thelowprokill/nerdboard/images/6.2/PXL_20240111_174422805.jpg

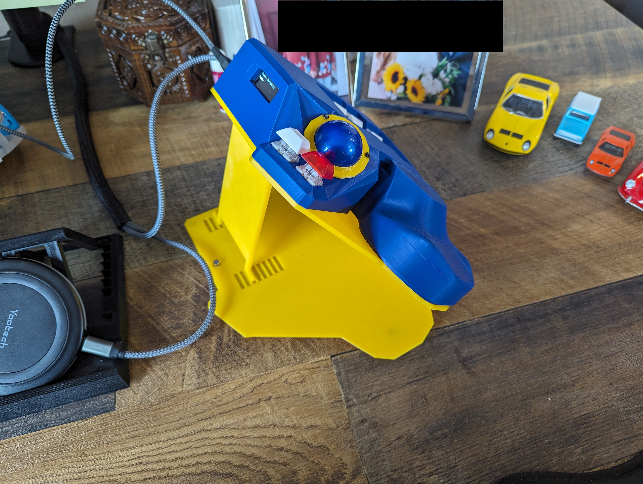
images/6.2/PXL_20240111_174422805.jpg
