thelowprokill/nerdboard/images/6.2/PXL_20240111_174425794.jpg

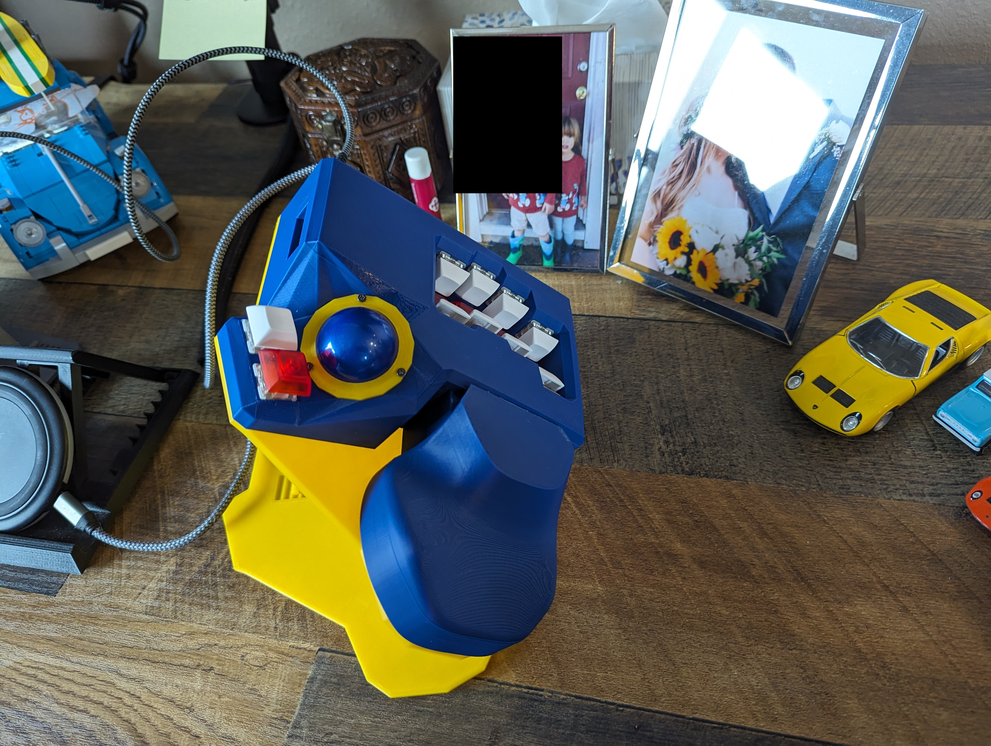
images/6.2/PXL_20240111_174425794.jpg
