thelowprokill/nerdboard/images/6.2/PXL_20240111_174430788.jpg

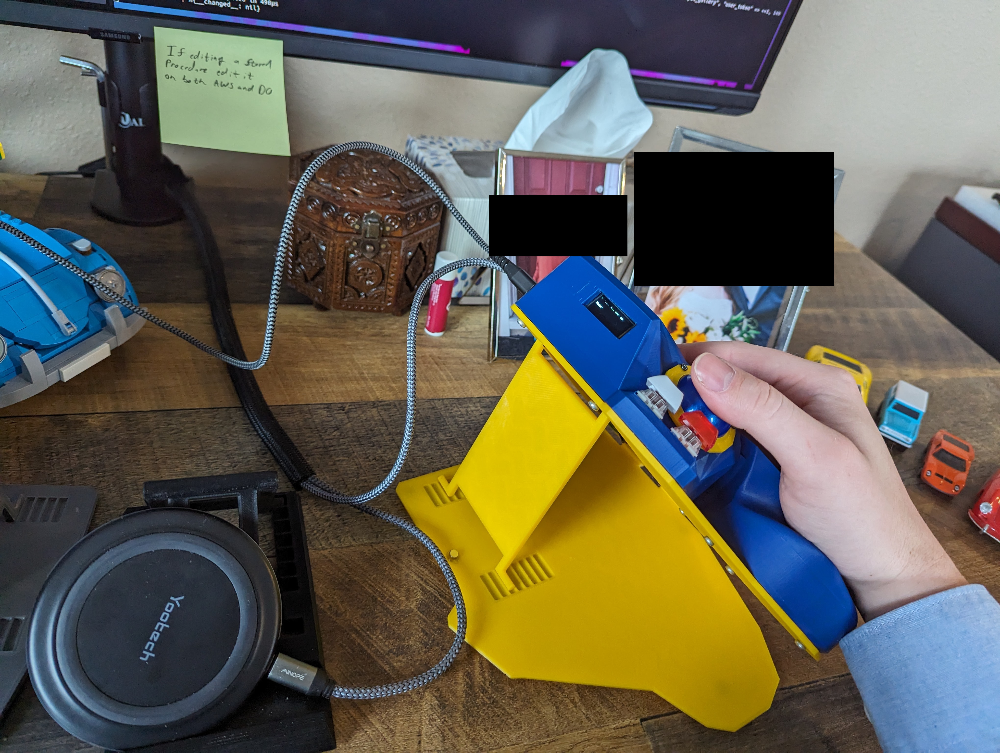
images/6.2/PXL_20240111_174430788.jpg
