thelowprokill/nerdboard/images/6.2/PXL_20240308_211952683.jpg

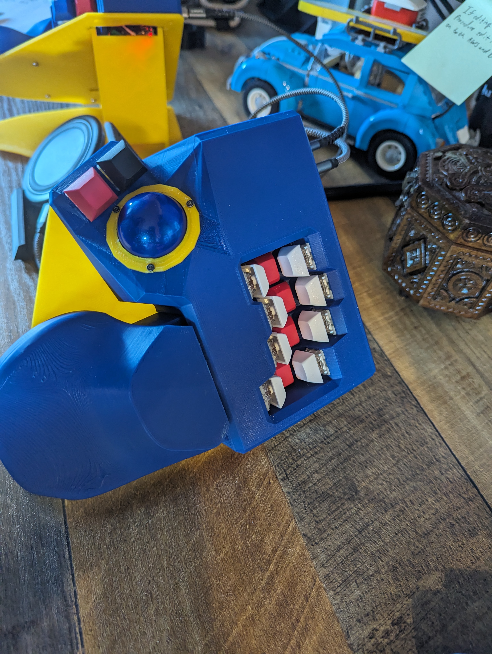
images/6.2/PXL_20240308_211952683.jpg
