thelowprokill/nerdboard/images/6.2/PXL_20240308_211957653.jpg

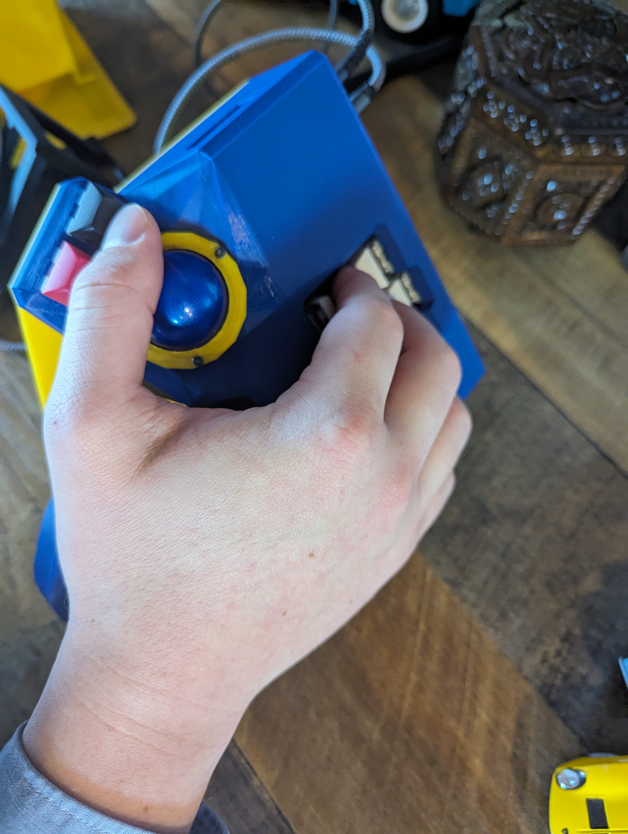
images/6.2/PXL_20240308_211957653.jpg
