thelowprokill/nerdboard/images/6.2/PXL_20240308_212002990.jpg

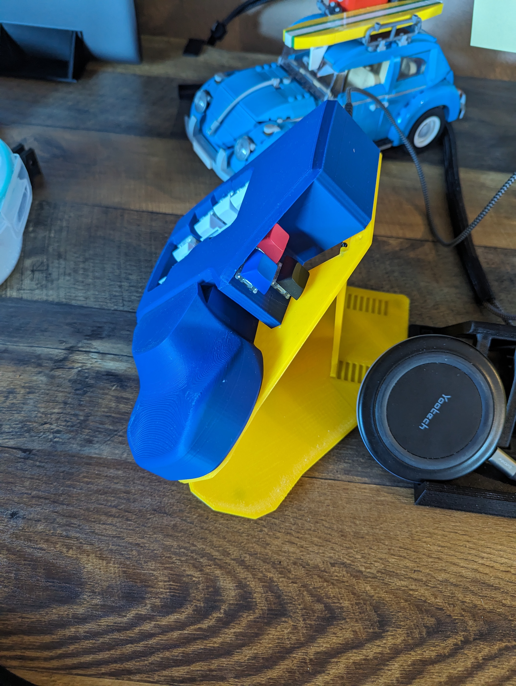
images/6.2/PXL_20240308_212002990.jpg
