thelowprokill/nerdboard/images/6.2/PXL_20240308_212005189.jpg

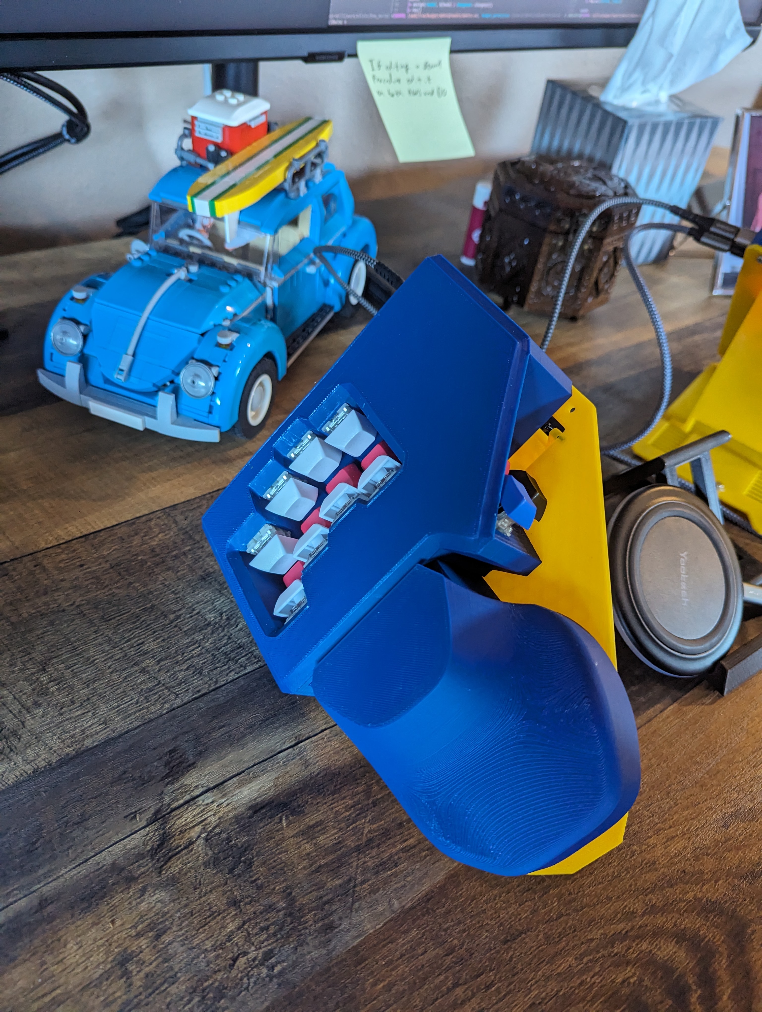
images/6.2/PXL_20240308_212005189.jpg
