thelowprokill/nerdboard/images/6.4/PXL_20260528_202627618.jpg

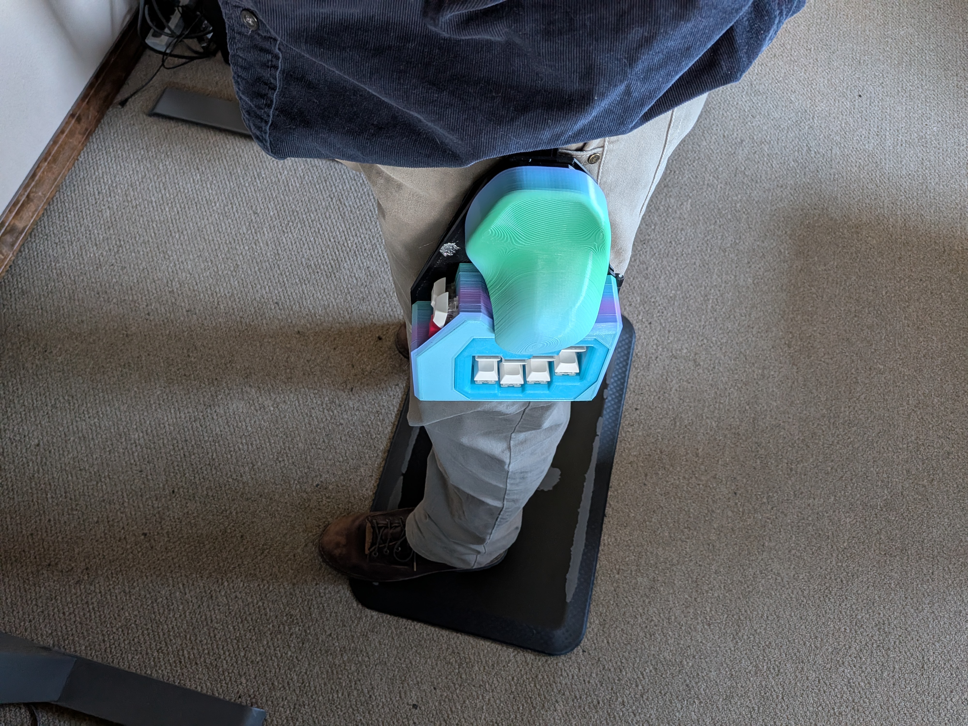
images/6.4/PXL_20260528_202627618.jpg
