thelowprokill/nerdboard/lp_01/lp_01_14.5mm.stl

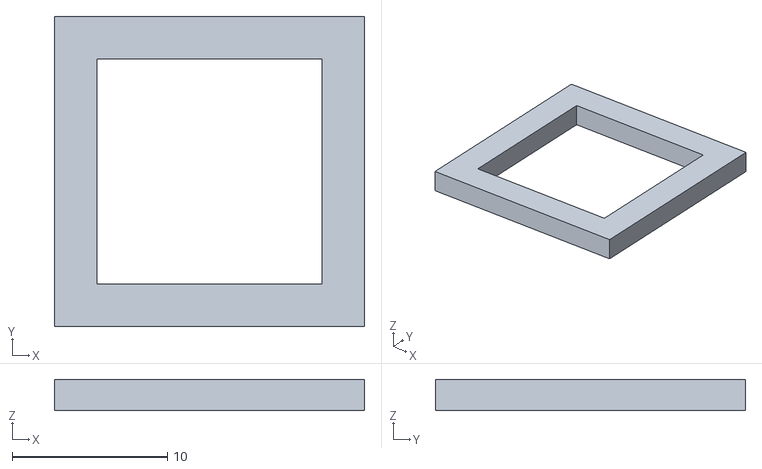
[picture p30: CAD file, 2024-03-11]
lp_01/lp_01_14.5mm.stl
20.0 x 20.0 x 2.00
