thelowprokill/nerdboard/parts/screen_negative.stl

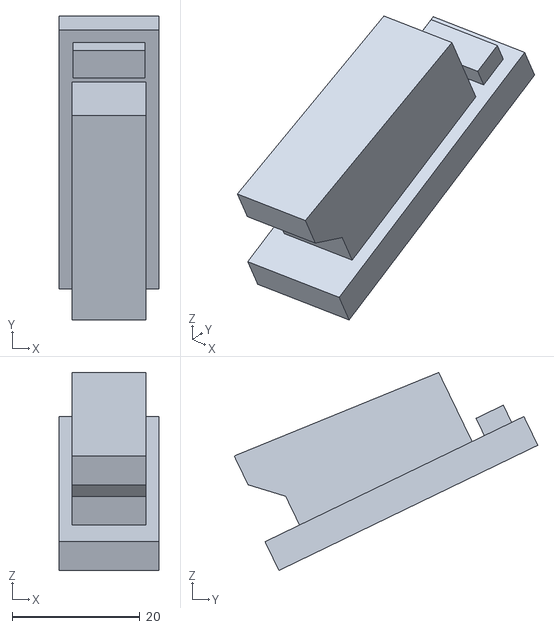
[picture p31: CAD file, 2023-07-21]
parts/screen_negative.stl
15.6 x 47.5 x 31.0
