thelowprokill/nerdboard/trackball_test/trackball_v3_ring_v2.stl

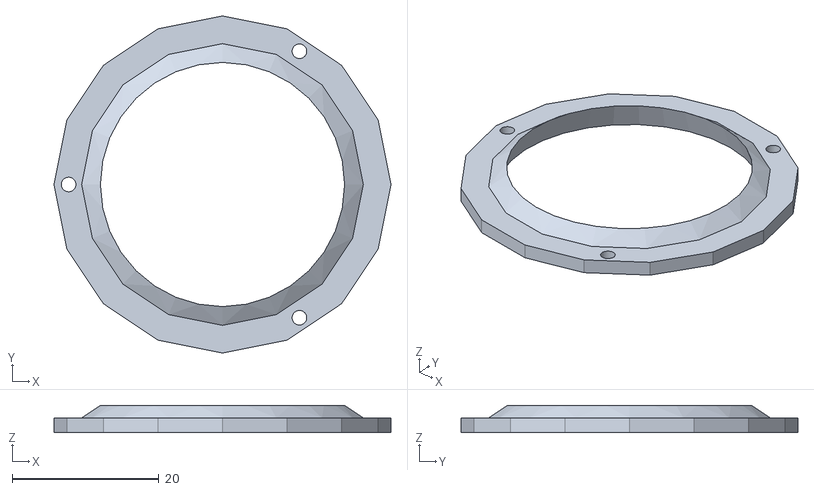
[picture p32: CAD file, 2024-03-11]
trackball_test/trackball_v3_ring_v2.stl
46.0 x 46.0 x 3.71
