thelowprokill/nerdboard/parts/io_positive.stl

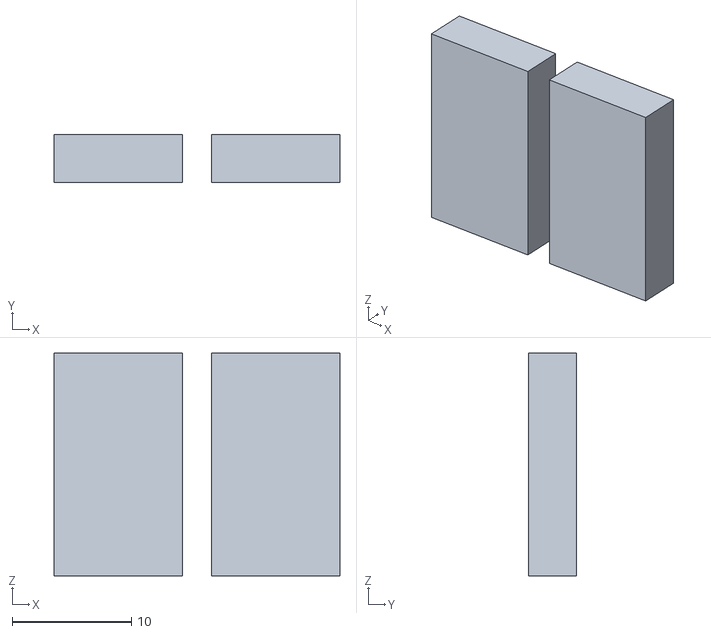
[picture p34: CAD file, 2023-07-21]
parts/io_positive.stl
24.0 x 4.00 x 18.7
