thelowprokill/nerdboard/lp_01/lp_01.stl

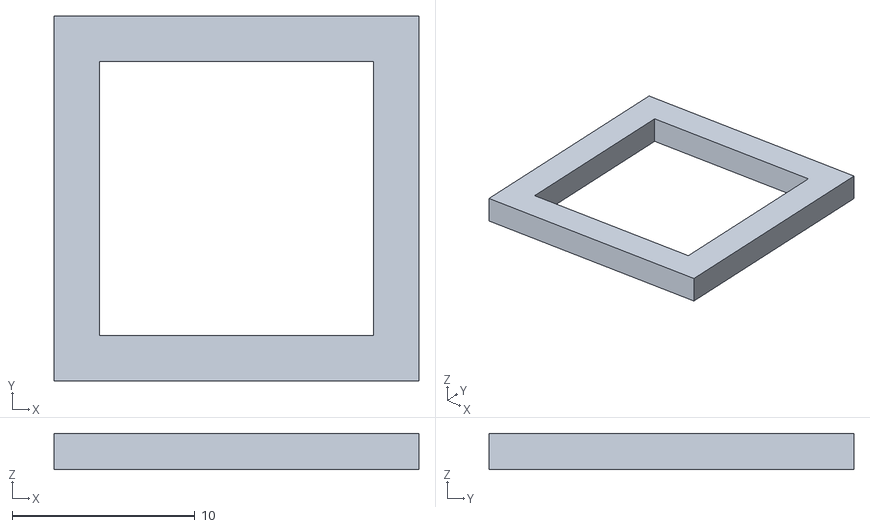
[picture p35: CAD file, 2024-03-11]
lp_01/lp_01.stl
20.0 x 20.0 x 2.00
