thelowprokill/nerdboard/parts/io_negative.stl

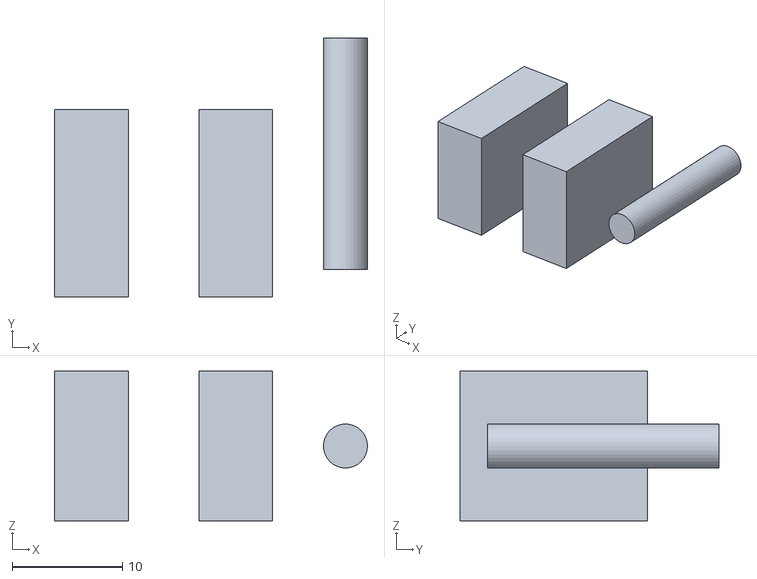
[picture p36: CAD file, 2023-07-21]
parts/io_negative.stl
28.4 x 23.5 x 13.6
