thelowprokill/nerdboard/trackball_test/trackball_v2_topper.stl

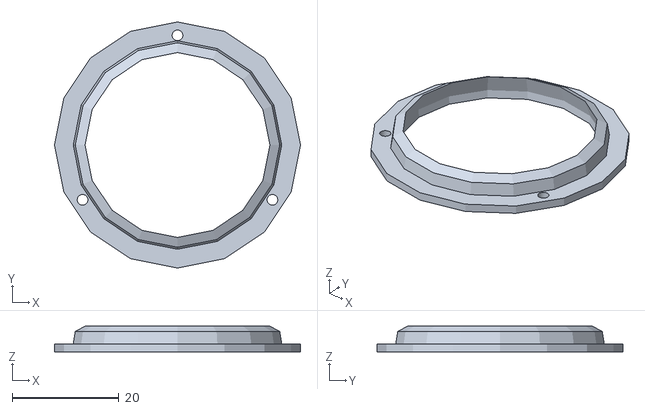
[picture p37: CAD file, 2024-01-10]
trackball_test/trackball_v2_topper.stl
46.0 x 46.0 x 4.82
