thelowprokill/nerdboard/lp_01/lp_horseshoe.stl

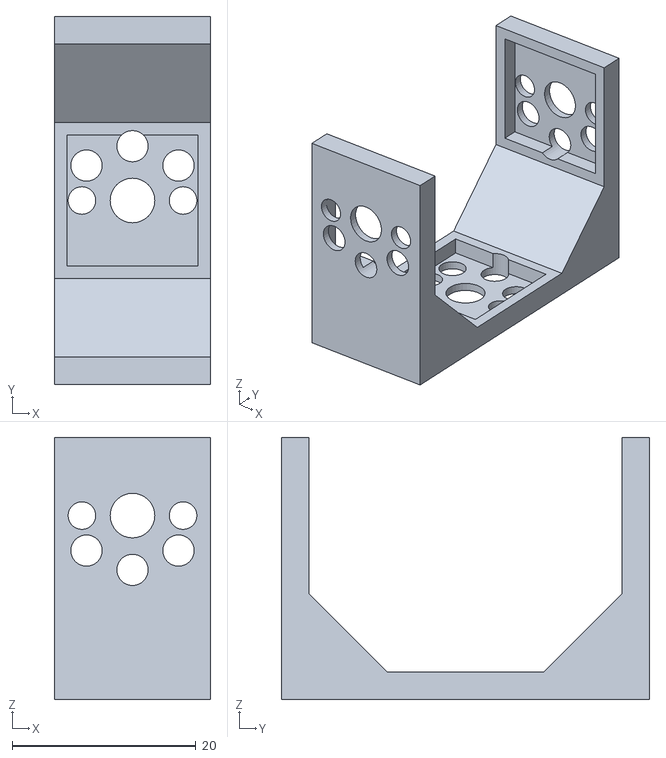
[picture p38: CAD file, 2024-03-11]
lp_01/lp_horseshoe.stl
17.0 x 40.0 x 28.5
