thelowprokill/nerdboard/trackball_test/trackball_test.stl

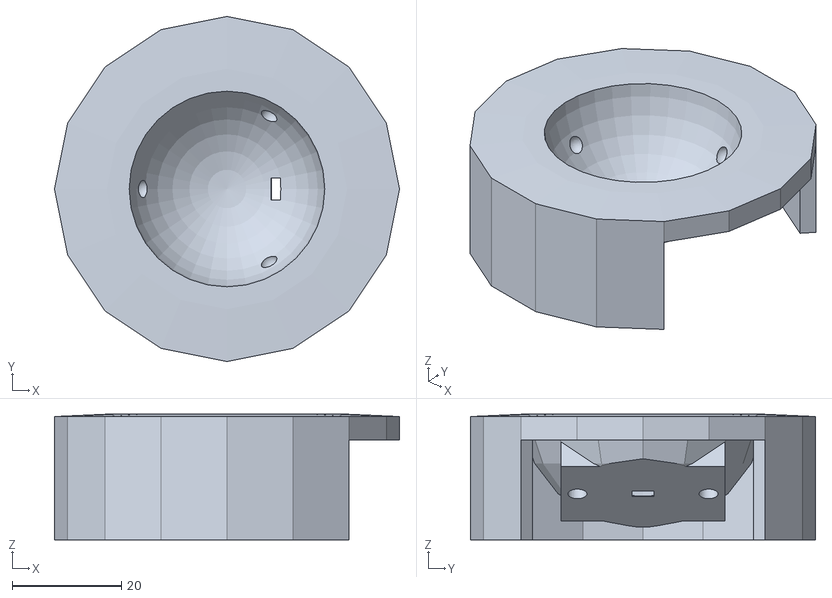
[picture p39: CAD file, 2024-01-10]
trackball_test/trackball_test.stl
63.1 x 63.1 x 23.0
