thelowprokill/nerdboard/lp_01/lp_spacing_test.stl

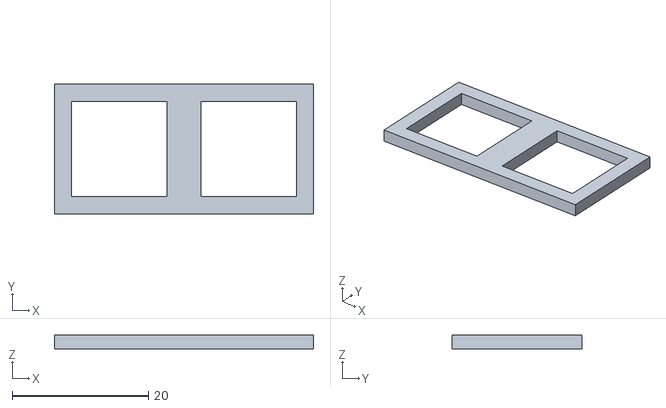
[picture p40: CAD file, 2024-03-11]
lp_01/lp_spacing_test.stl
38.0 x 19.0 x 2.00
