thelowprokill/nerdboard/parts/vertical_test.stl

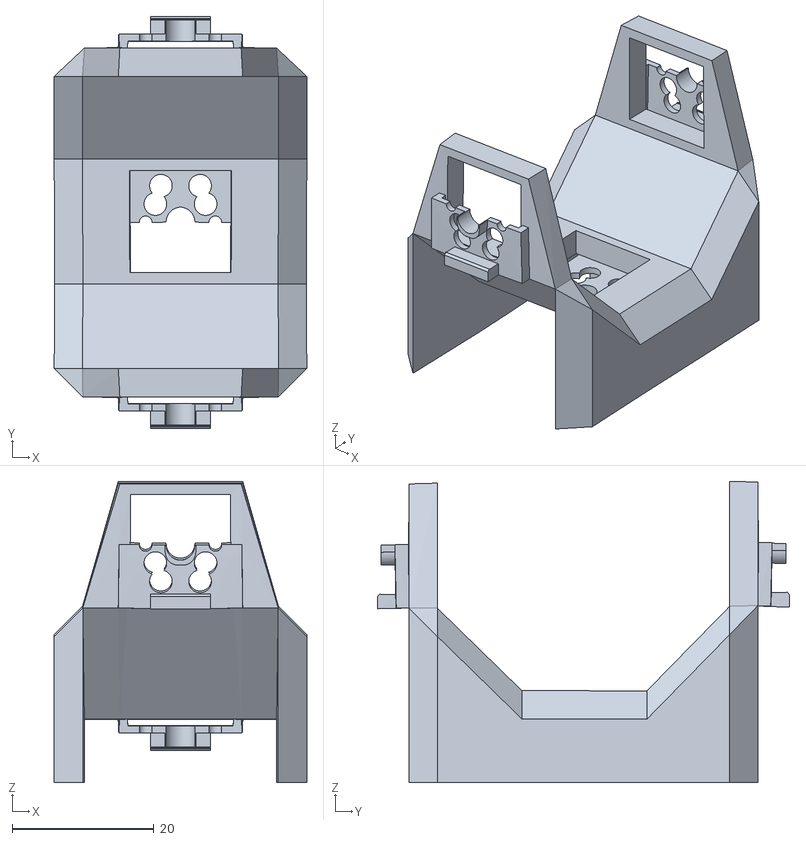
[picture p41: CAD file, 2023-07-19]
parts/vertical_test.stl
35.7 x 58.2 x 42.6
