thelowprokill/nerdboard/trackball_test/trackball_v3_ring_v1.stl

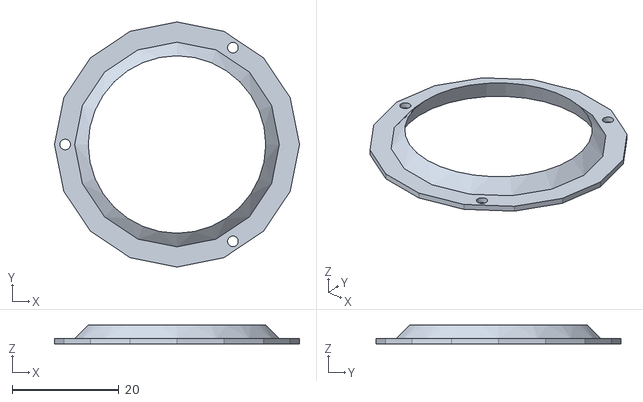
[picture p42: CAD file, 2024-01-10]
trackball_test/trackball_v3_ring_v1.stl
46.0 x 46.0 x 3.51
