thelowprokill/nerdboard/trackball_test/trackball_v2_topper_v5.stl

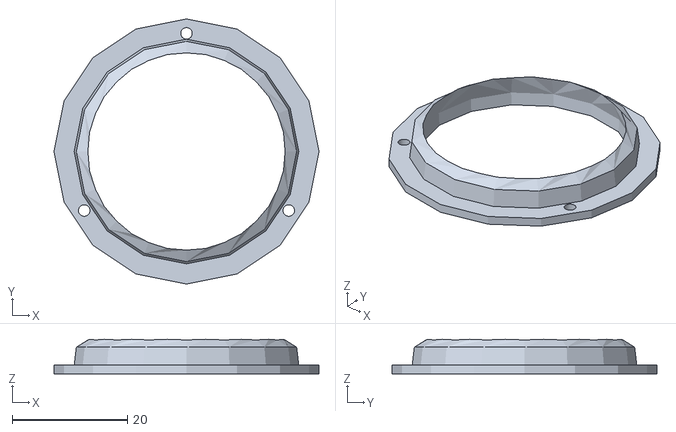
[picture p43: CAD file, 2024-01-10]
trackball_test/trackball_v2_topper_v5.stl
46.0 x 46.0 x 5.99
