thelowprokill/nerdboard/parts/mouse_bowl.stl

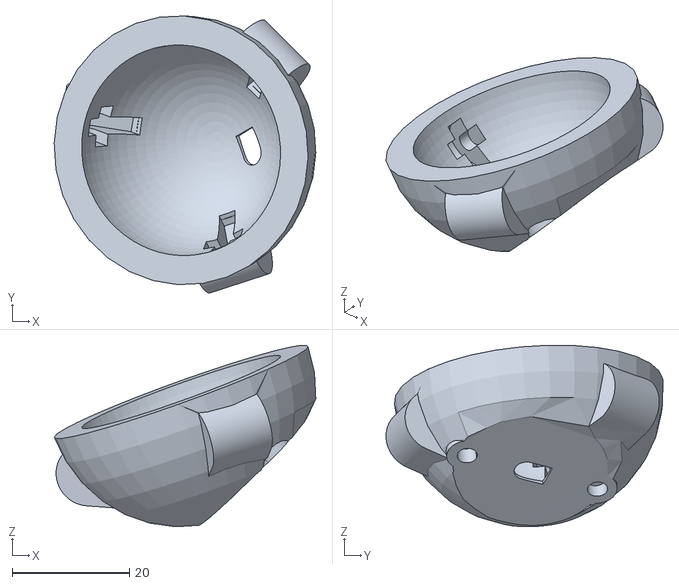
[picture p44: CAD file, 2023-07-19]
parts/mouse_bowl.stl
44.6 x 47.2 x 30.9
