thelowprokill/nerdboard/trackball_test/trackball_v2_topper_v4.stl

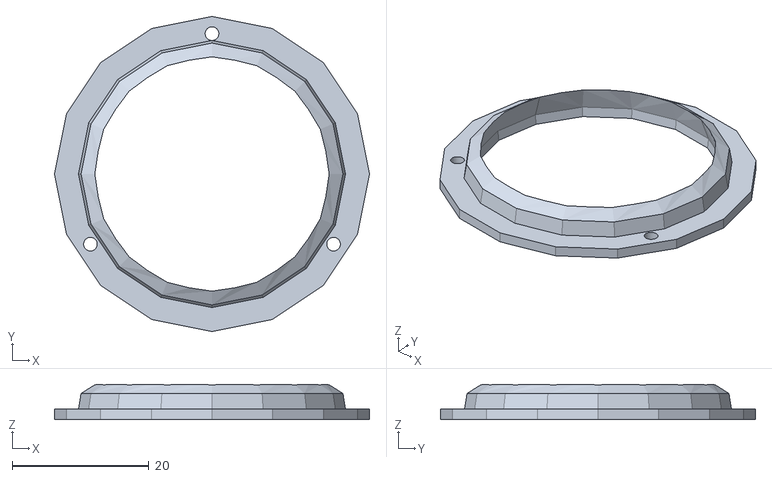
[picture p45: CAD file, 2024-01-10]
trackball_test/trackball_v2_topper_v4.stl
46.0 x 46.0 x 5.12
