thelowprokill/nerdboard/trackball_test/trackball_v2_topper_v3.stl

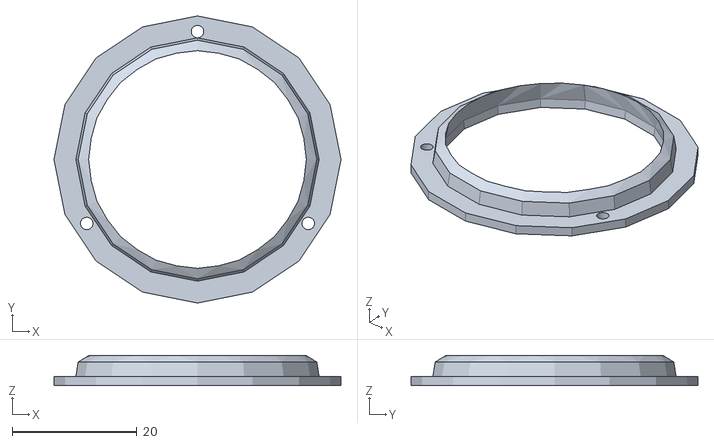
[picture p46: CAD file, 2024-01-10]
trackball_test/trackball_v2_topper_v3.stl
46.0 x 46.0 x 4.89
