thelowprokill/nerdboard/trackball_test/trackball_v2_topper_v6.stl

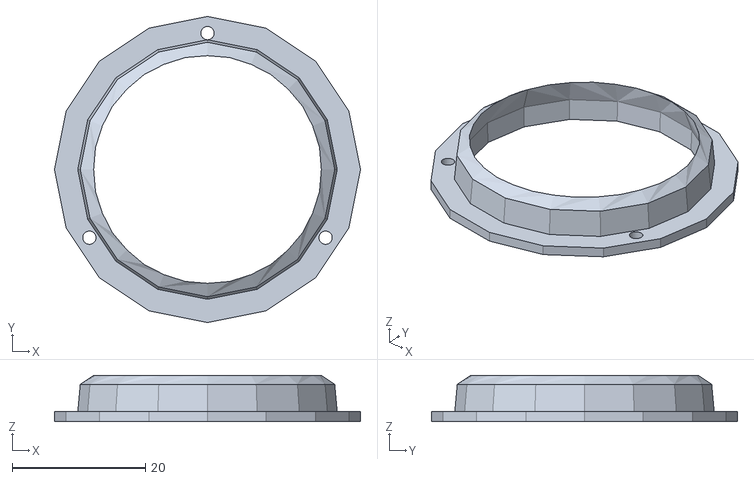
[picture p47: CAD file, 2024-01-10]
trackball_test/trackball_v2_topper_v6.stl
46.0 x 46.0 x 6.93
